minhazislamnafi/KEEBY60-20/DOCS/Screenshot 2026-05-22 185201 - Copy.png

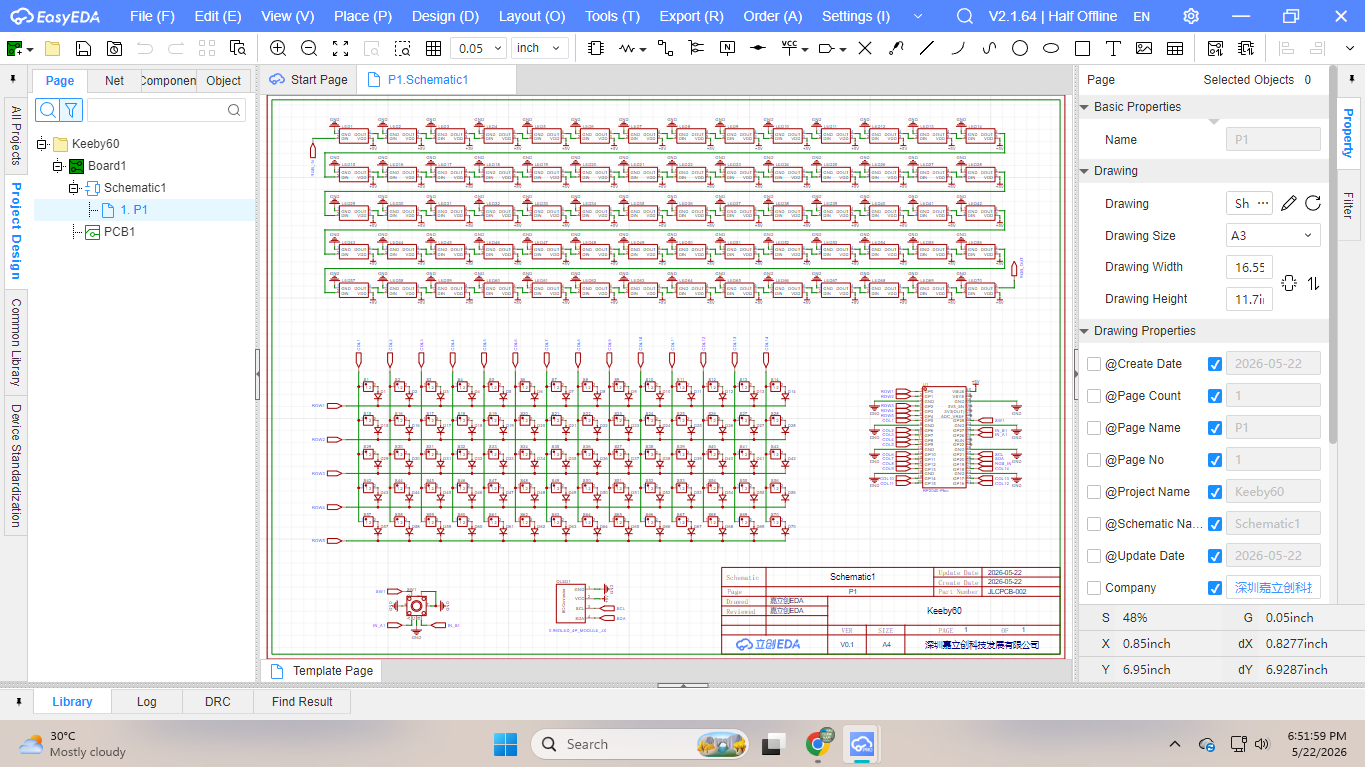
DOCS/Screenshot 2026-05-22 185201 - Copy.png
