minhazislamnafi/KEEBY60-20/DOCS/Screenshot 2026-05-22 223106 - Copy.png

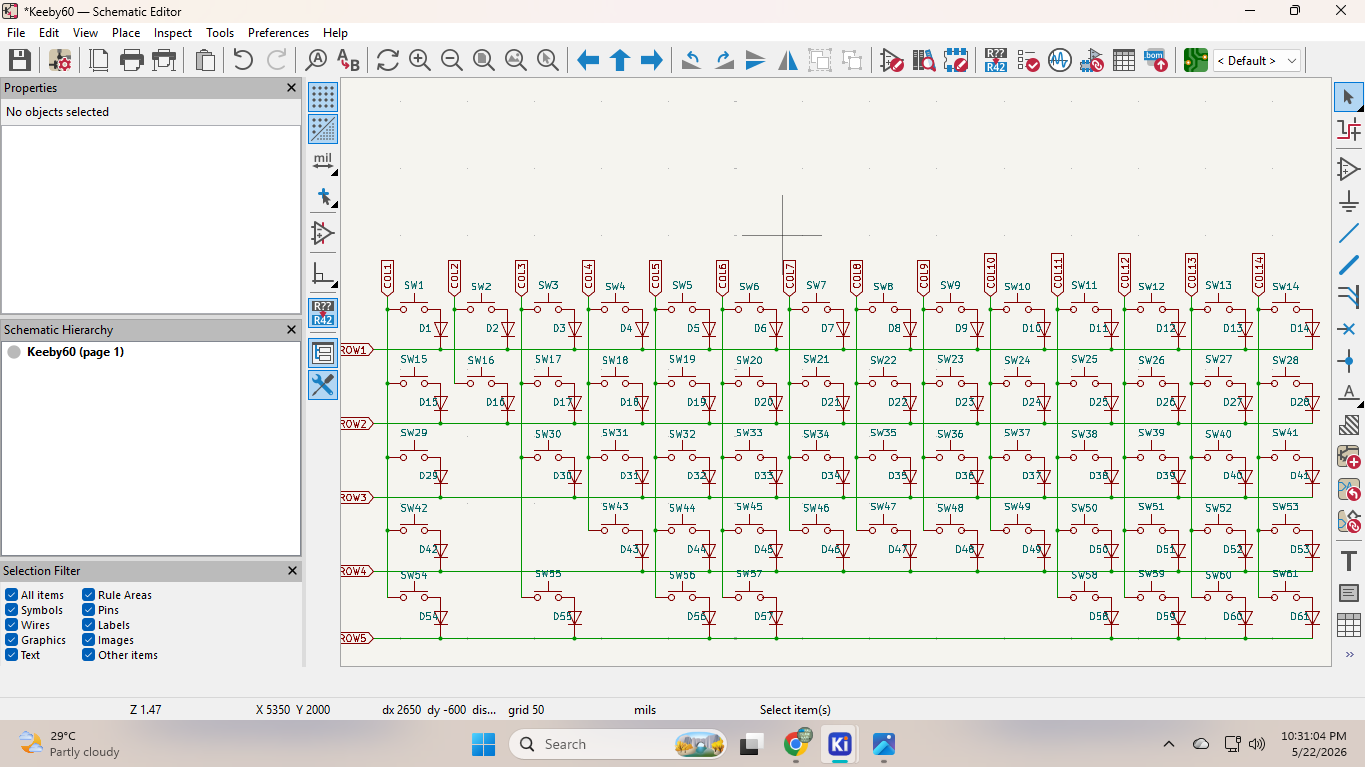
DOCS/Screenshot 2026-05-22 223106 - Copy.png
