minhazislamnafi/KEEBY60-20/DOCS/Screenshot 2026-05-23 002941 - Copy.png

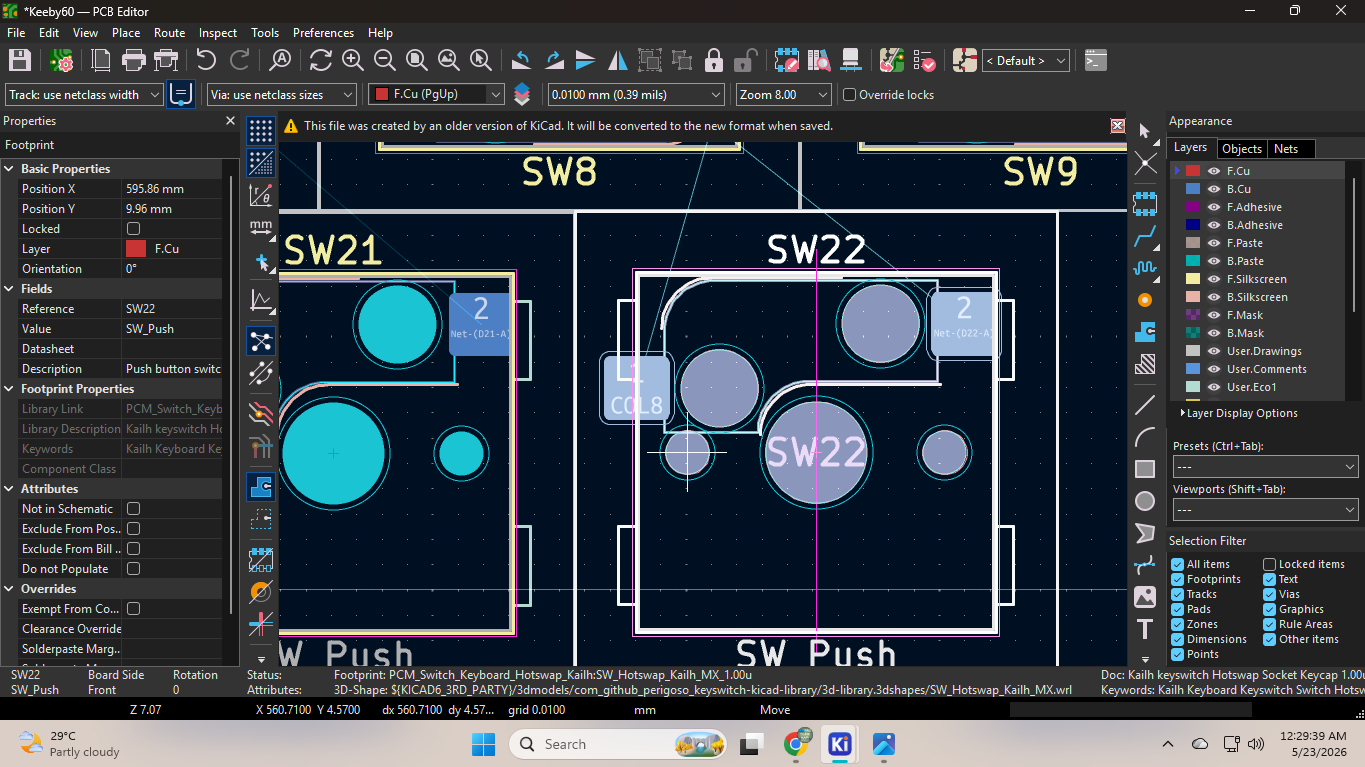
DOCS/Screenshot 2026-05-23 002941 - Copy.png
