minhazislamnafi/KEEBY60-20/DOCS/Screenshot 2026-05-23 003102 - Copy.png

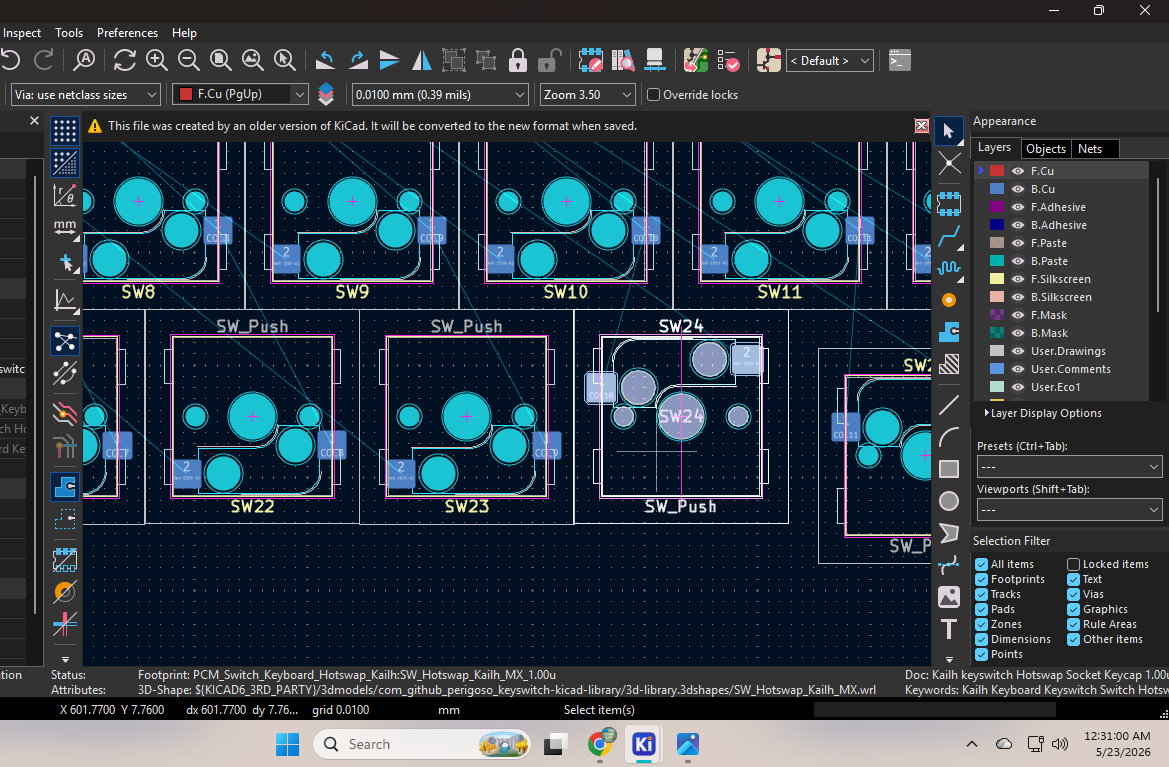
DOCS/Screenshot 2026-05-23 003102 - Copy.png
