minhazislamnafi/KEEBY60-20/DOCS/Screenshot 2026-05-23 170219.png

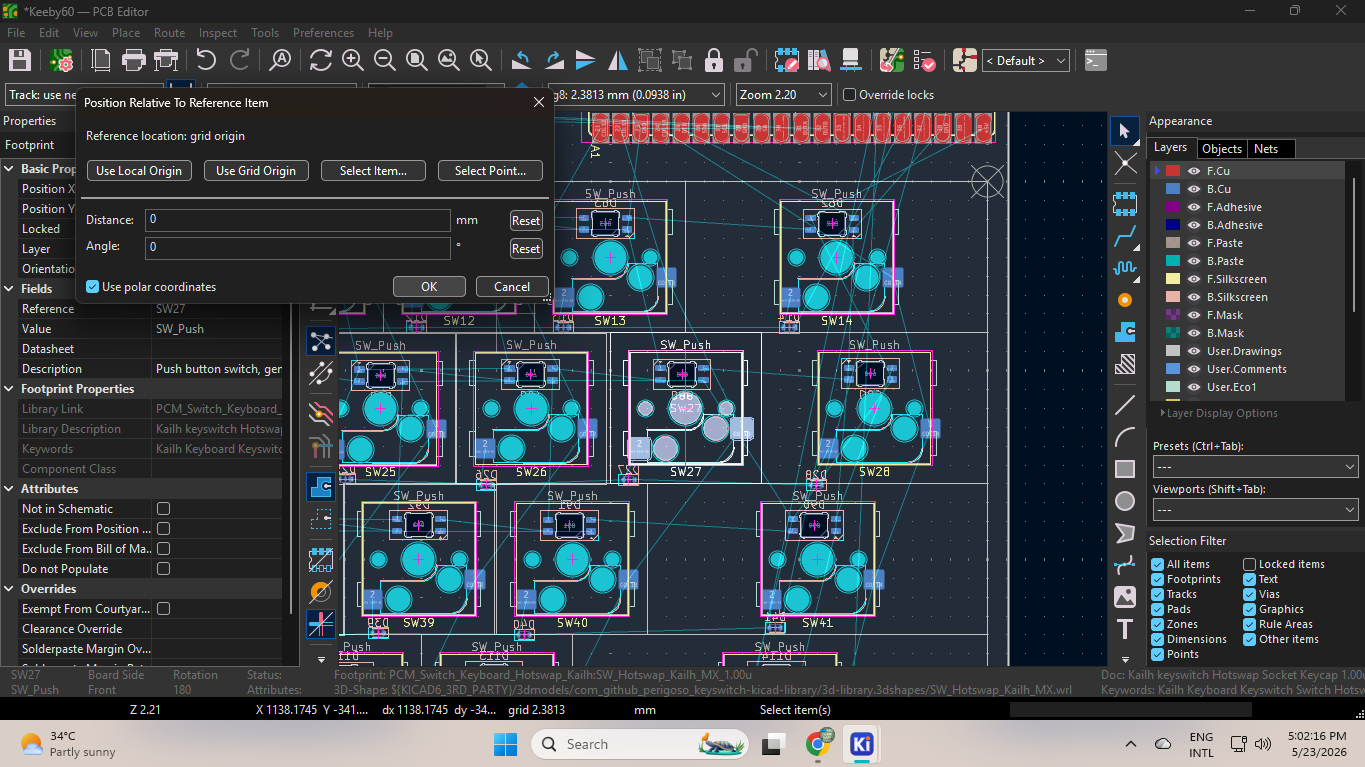
DOCS/Screenshot 2026-05-23 170219.png
