minhazislamnafi/KEEBY60-20/DOCS/Screenshot 2026-05-23 170231.png

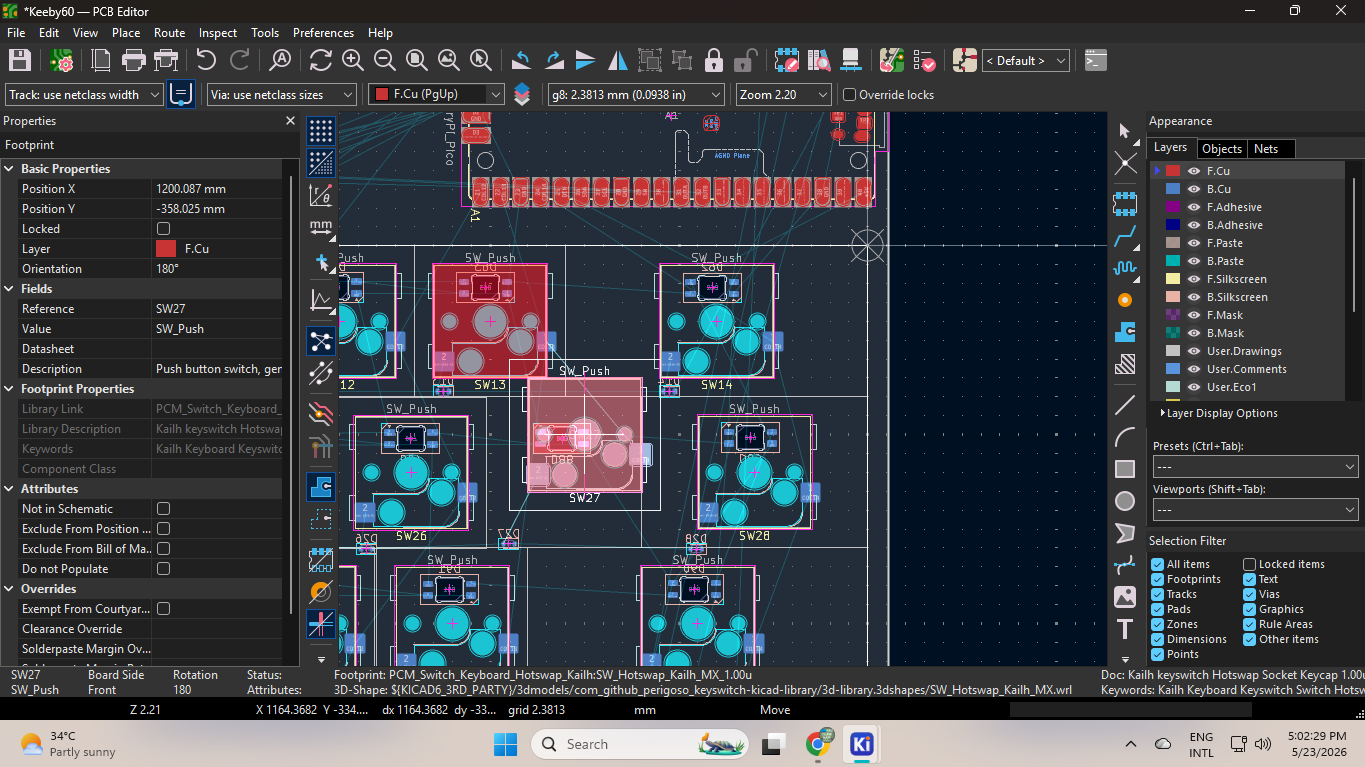
DOCS/Screenshot 2026-05-23 170231.png
