minhazislamnafi/KEEBY60-20/DOCS/Screenshot 2026-05-24 041032.png

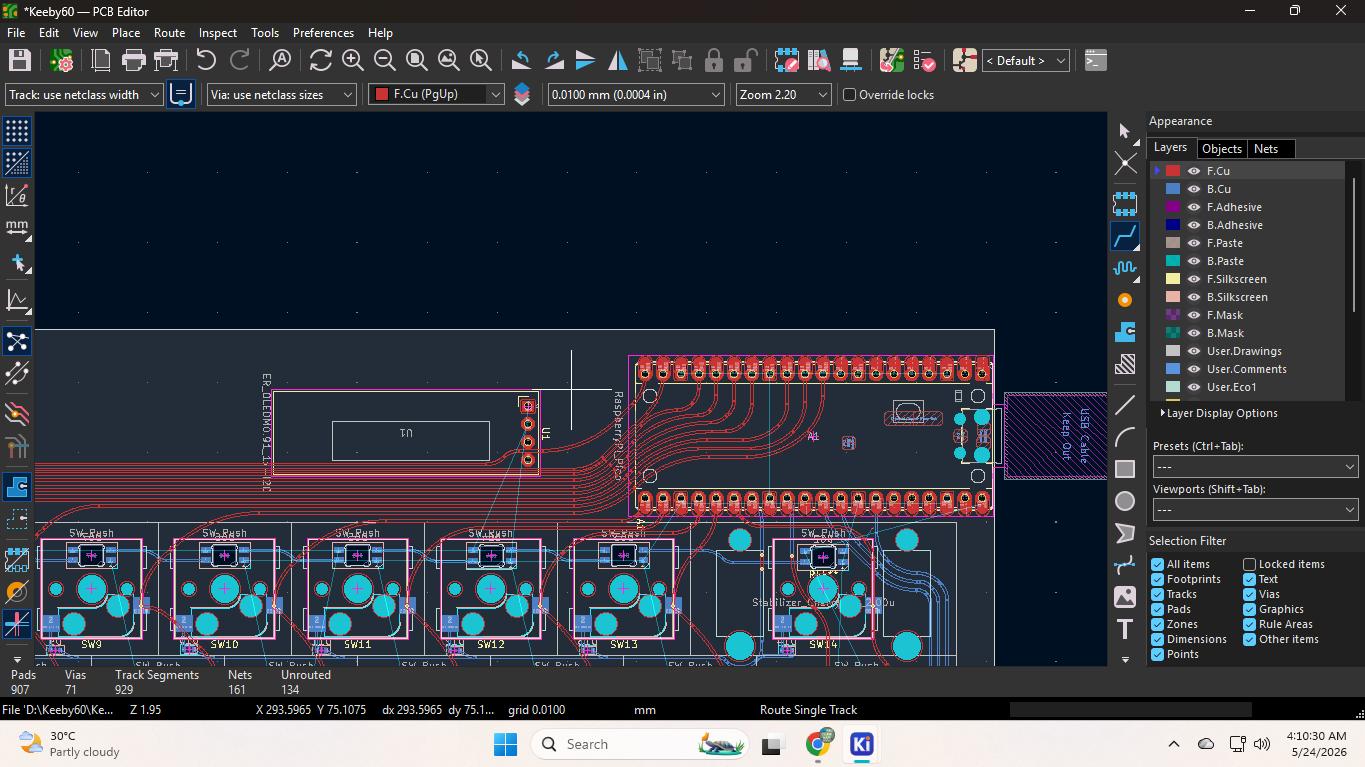
DOCS/Screenshot 2026-05-24 041032.png
