minhazislamnafi/KEEBY60-20/DOCS/Screenshot 2026-05-25 170520.png

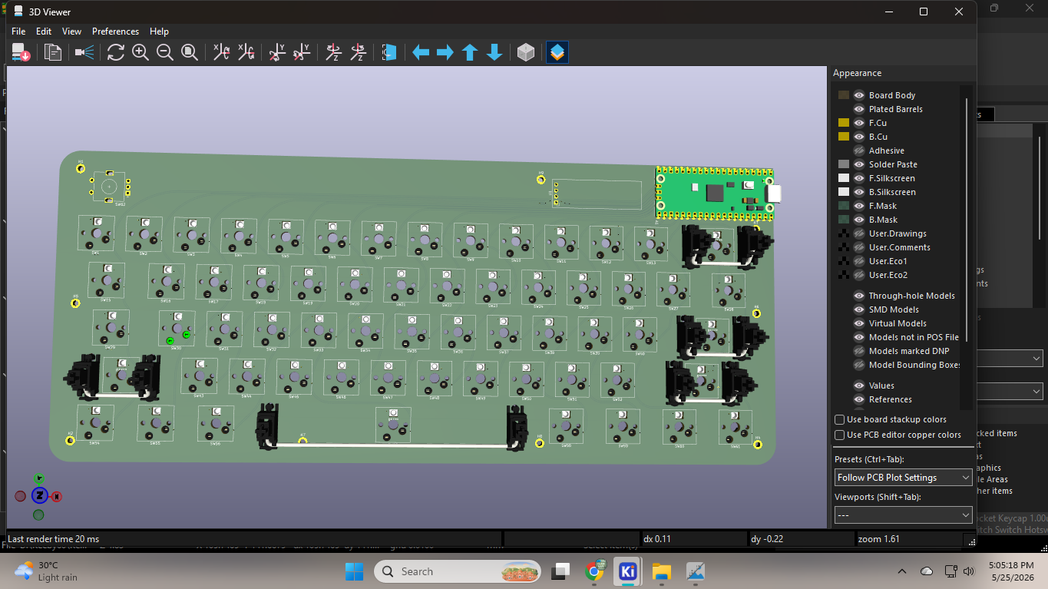
DOCS/Screenshot 2026-05-25 170520.png
