minhazislamnafi/KEEBY60-20/DOCS/Screenshot 2026-05-25 233830.png

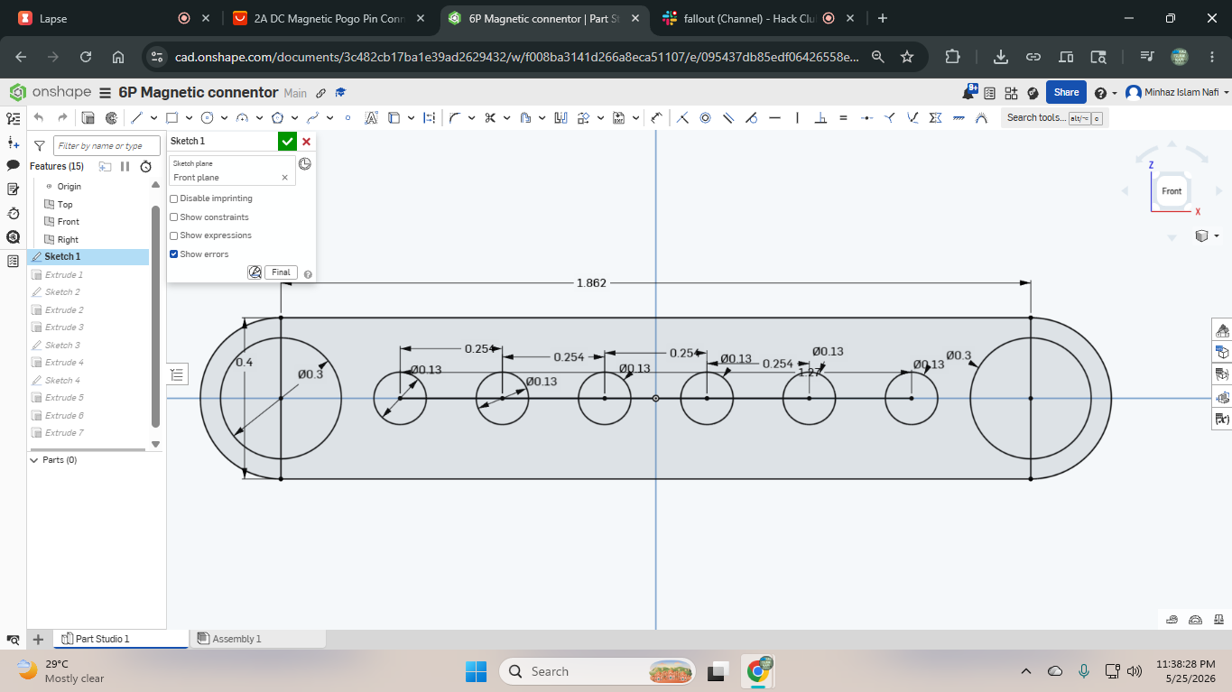
DOCS/Screenshot 2026-05-25 233830.png
