minhazislamnafi/KEEBY60-20/DOCS/Screenshot 2026-05-26 022730.png

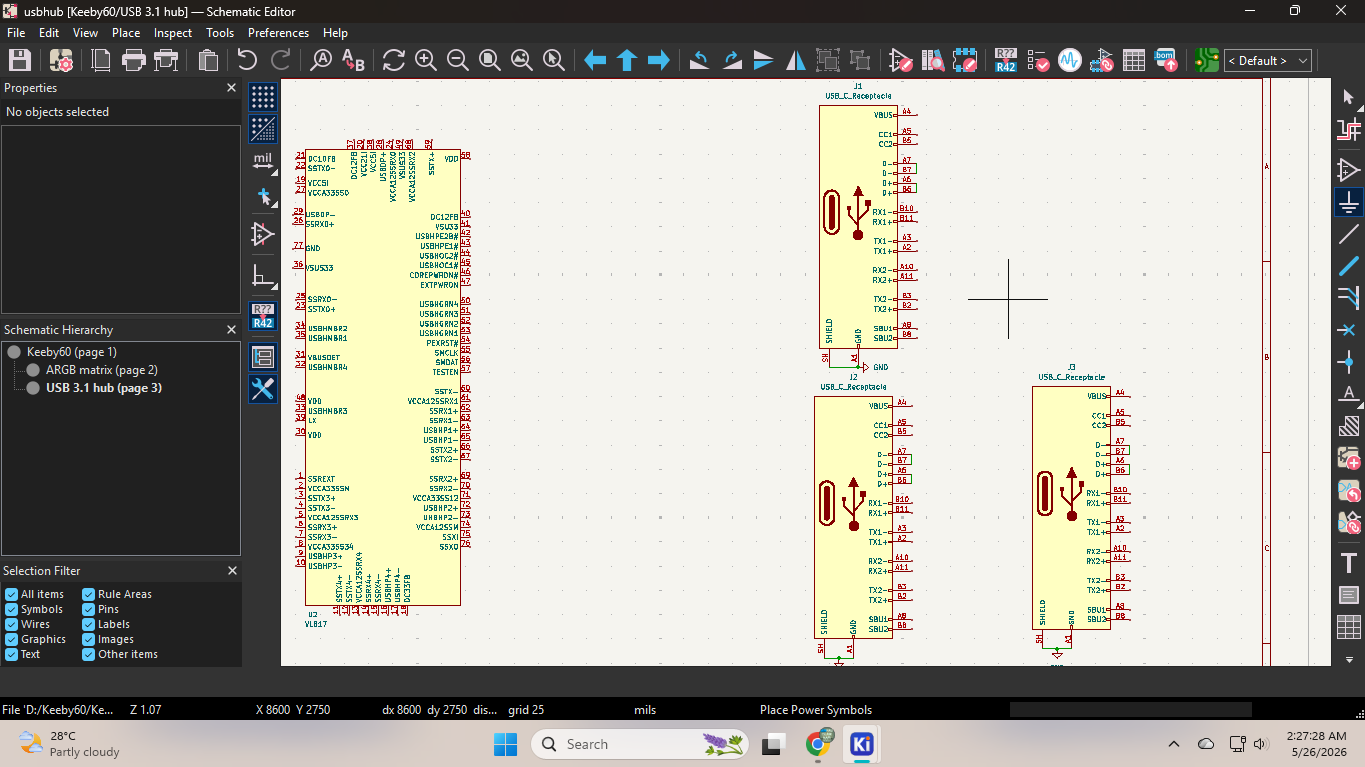
DOCS/Screenshot 2026-05-26 022730.png
