minhazislamnafi/KEEBY60-20/DOCS/Screenshot 2026-05-26 030540.png

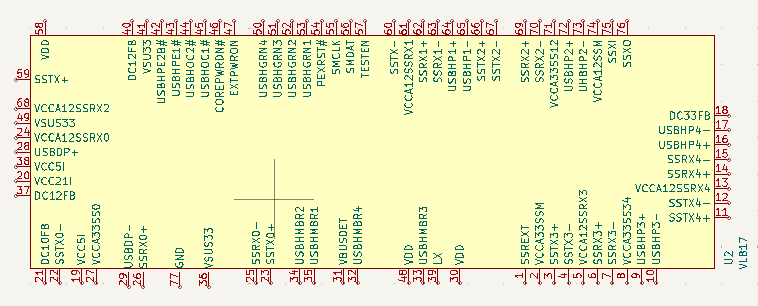
DOCS/Screenshot 2026-05-26 030540.png
