minhazislamnafi/KEEBY60-20/DOCS/Screenshot 2026-05-26 162601.png

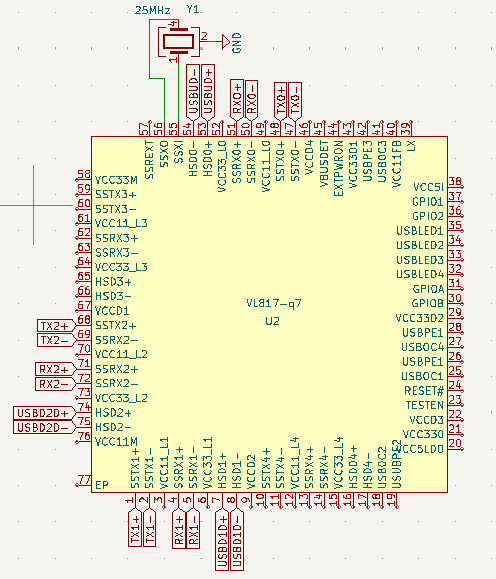
DOCS/Screenshot 2026-05-26 162601.png
