minhazislamnafi/KEEBY60-20/DOCS/Screenshot 2026-05-26 165118.png

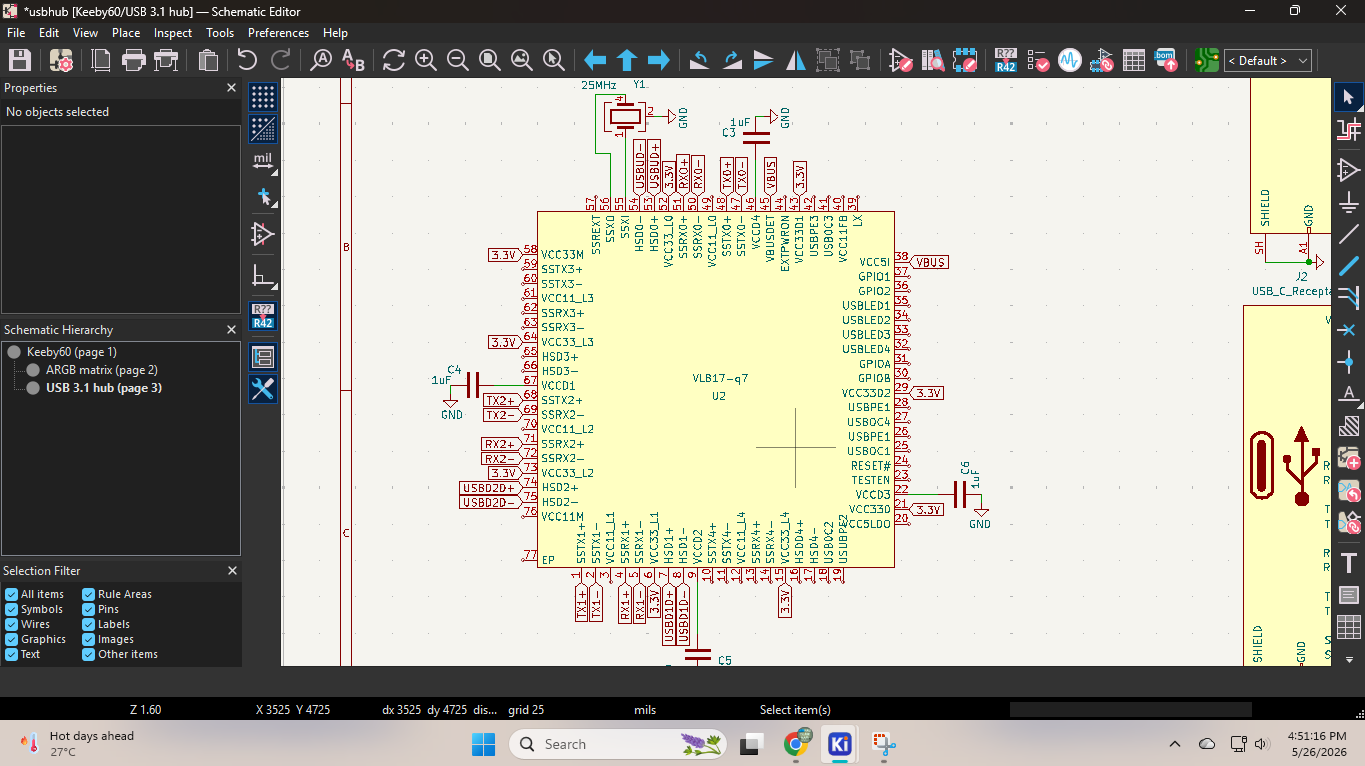
DOCS/Screenshot 2026-05-26 165118.png
