minhazislamnafi/KEEBY60-20/DOCS/Screenshot 2026-05-26 190104.png

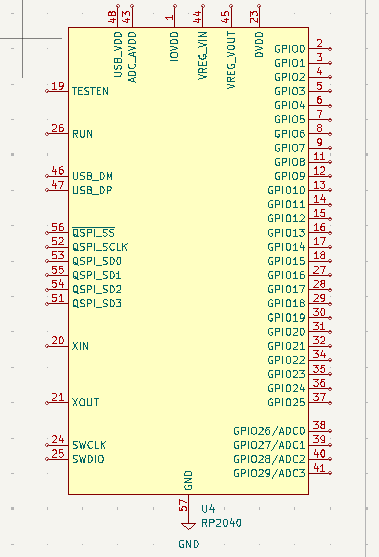
DOCS/Screenshot 2026-05-26 190104.png
