minhazislamnafi/KEEBY60-20/DOCS/Screenshot 2026-05-26 202656.png

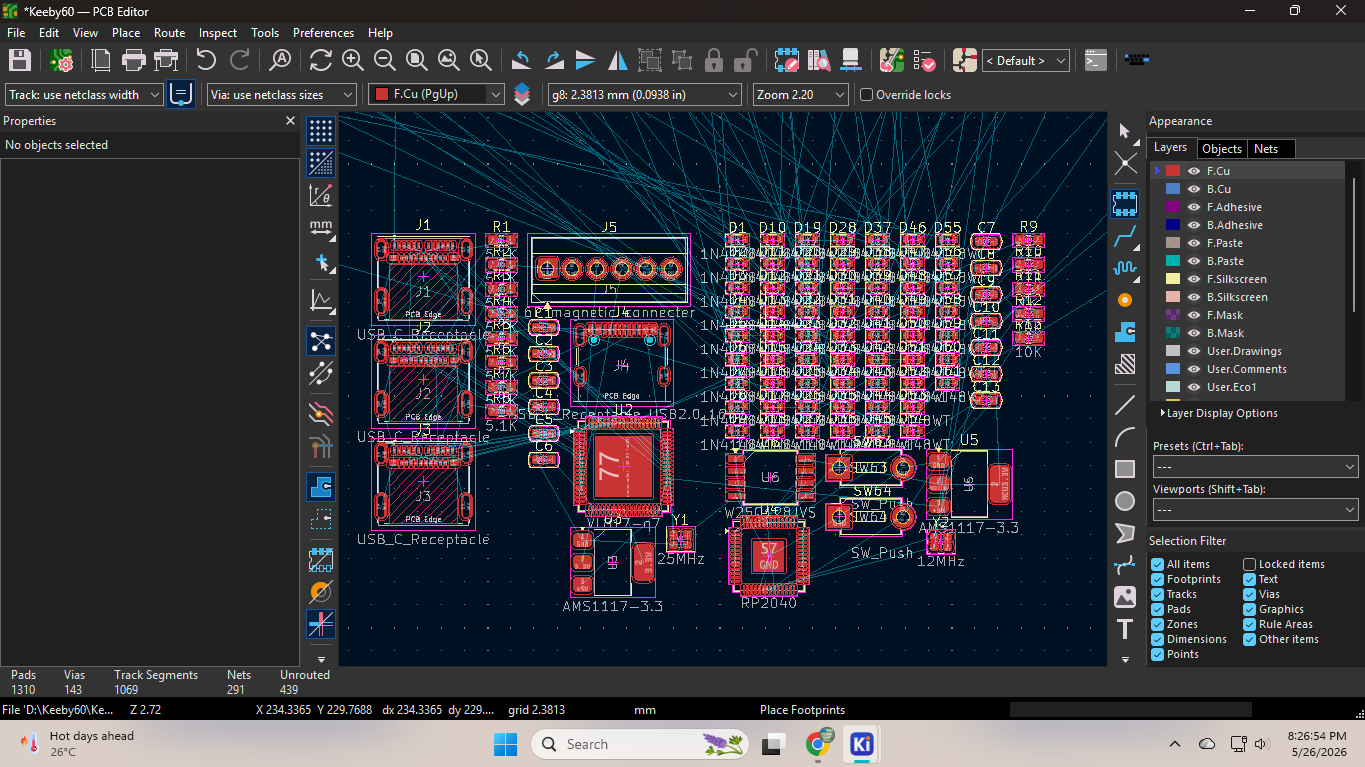
DOCS/Screenshot 2026-05-26 202656.png
