minhazislamnafi/KEEBY60-20/DOCS/Screenshot 2026-05-27 020248.png

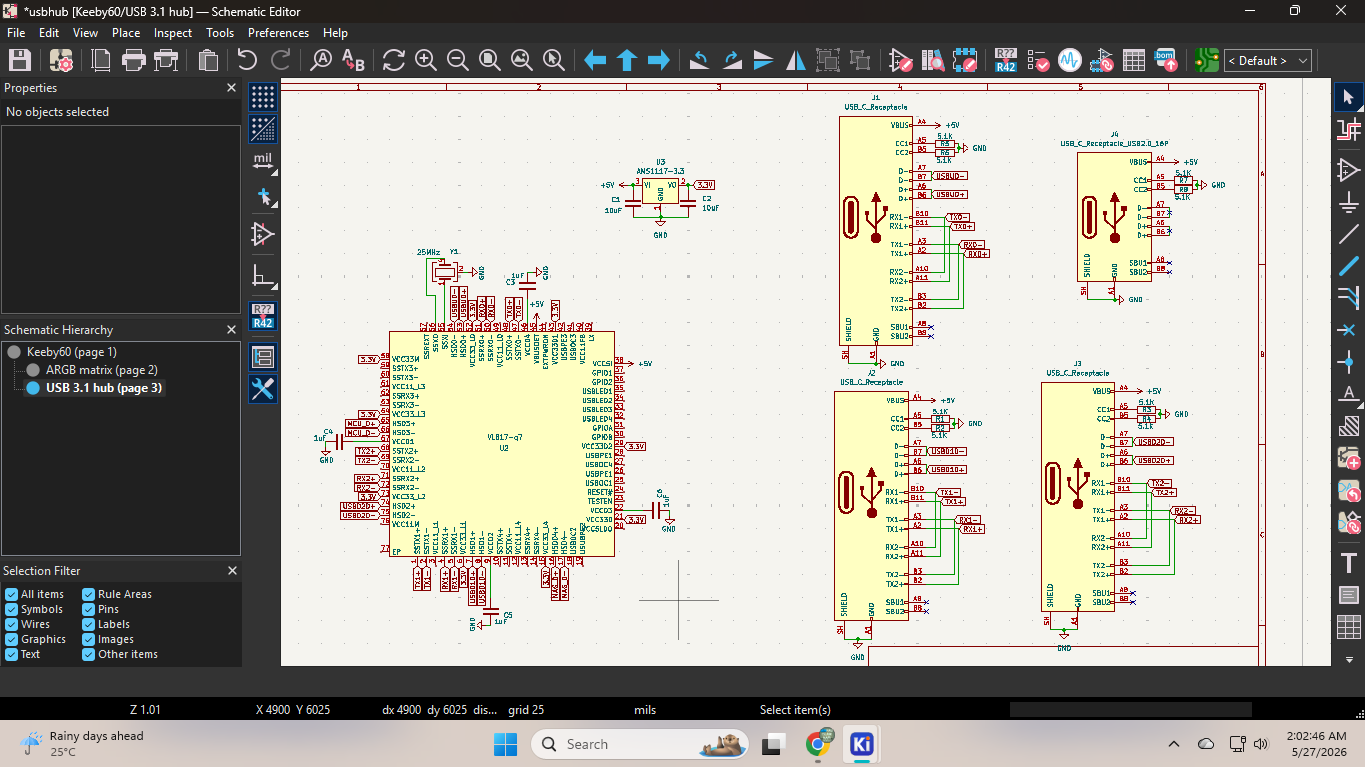
DOCS/Screenshot 2026-05-27 020248.png
