minhazislamnafi/KEEBY60-20/DOCS/Screenshot 2026-05-27 023414.png

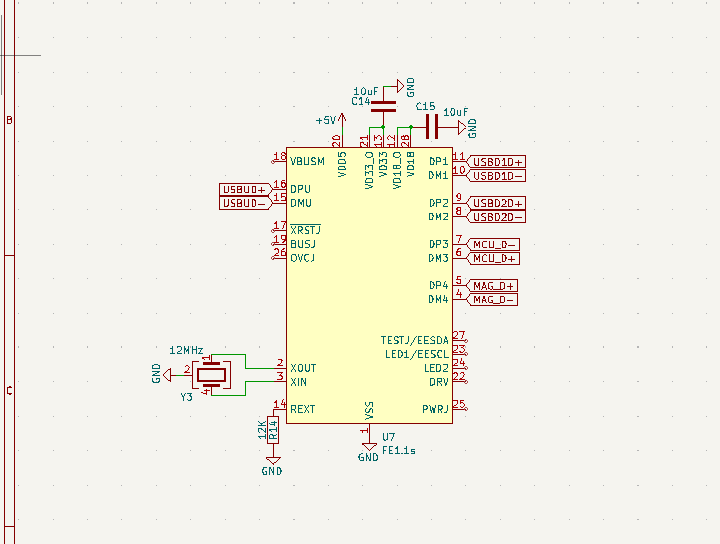
DOCS/Screenshot 2026-05-27 023414.png
