minhazislamnafi/KEEBY60-20/DOCS/Screenshot 2026-05-27 215645.png

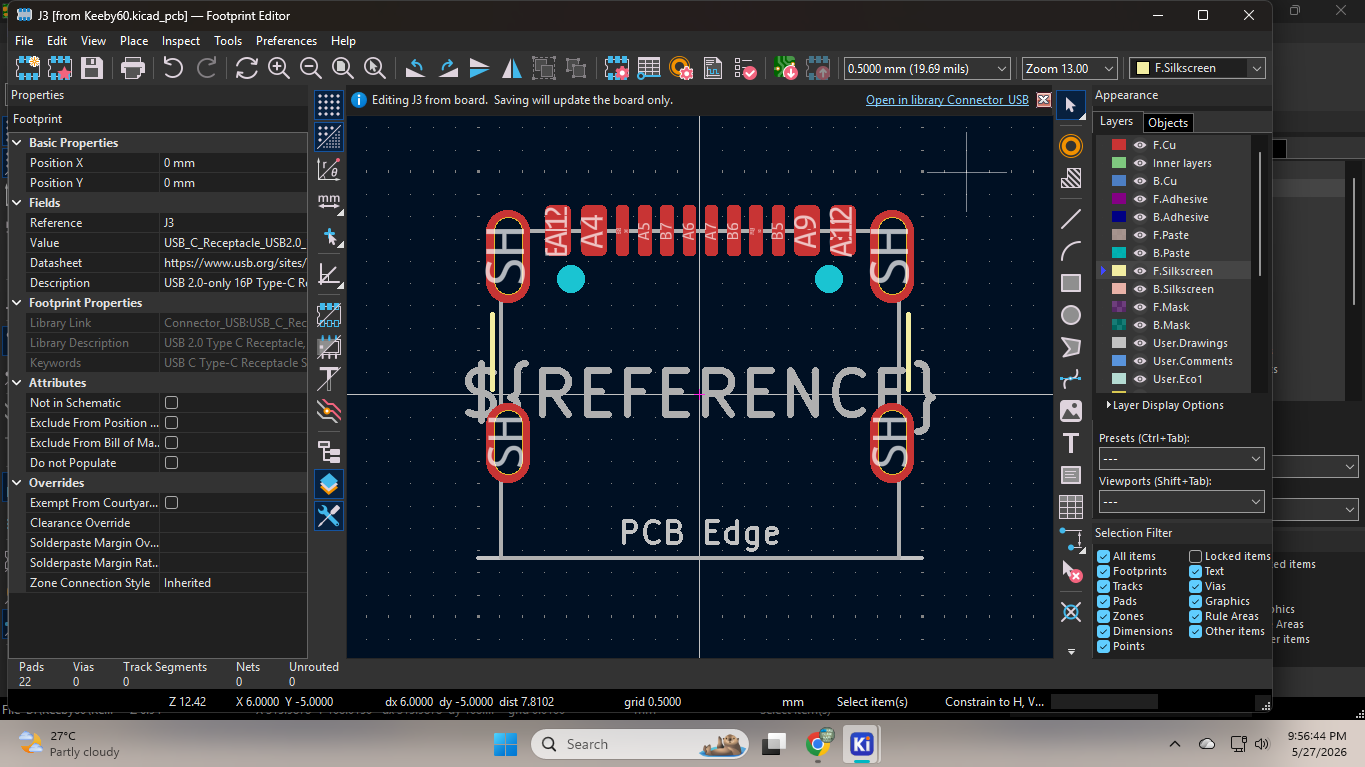
DOCS/Screenshot 2026-05-27 215645.png
