minhazislamnafi/KEEBY60-20/DOCS/Screenshot 2026-05-28 121309.png

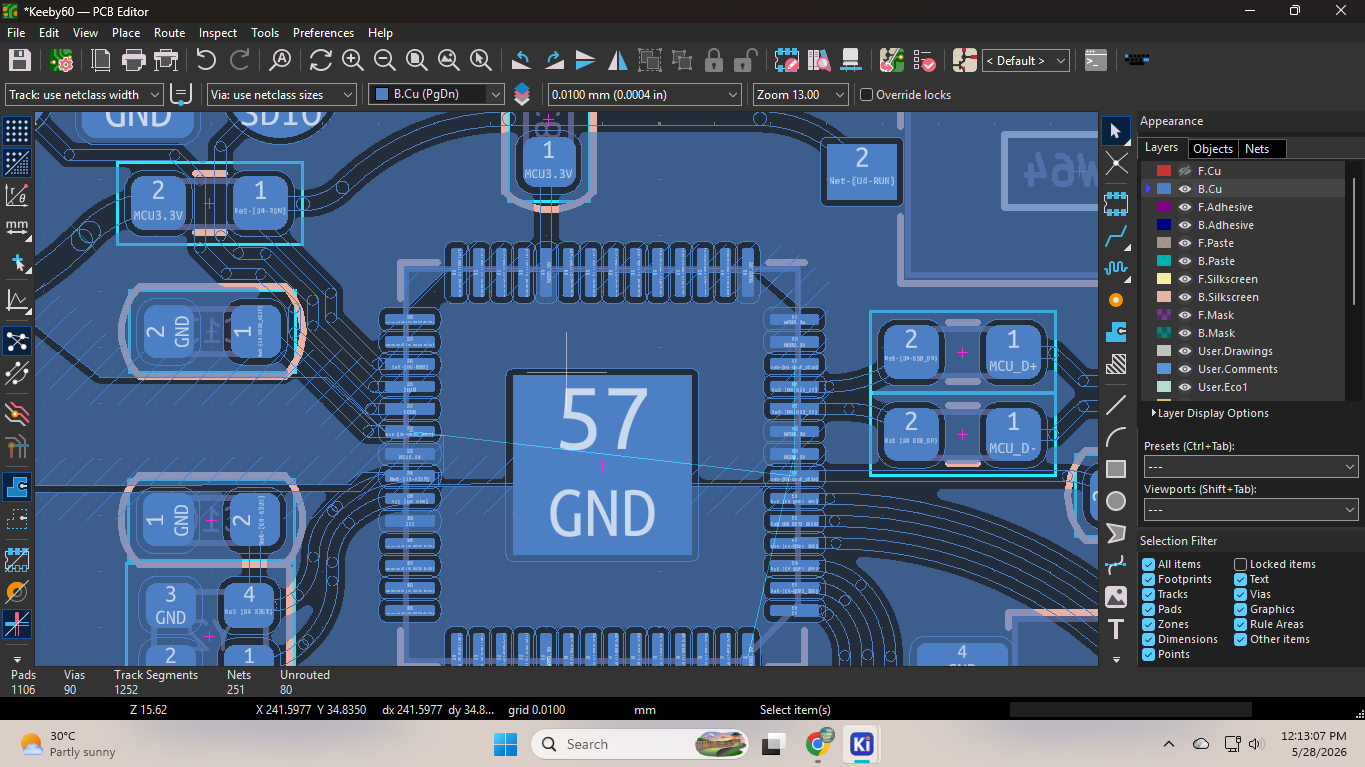
DOCS/Screenshot 2026-05-28 121309.png
