minhazislamnafi/KEEBY60-20/DOCS/Screenshot 2026-05-28 133856.png

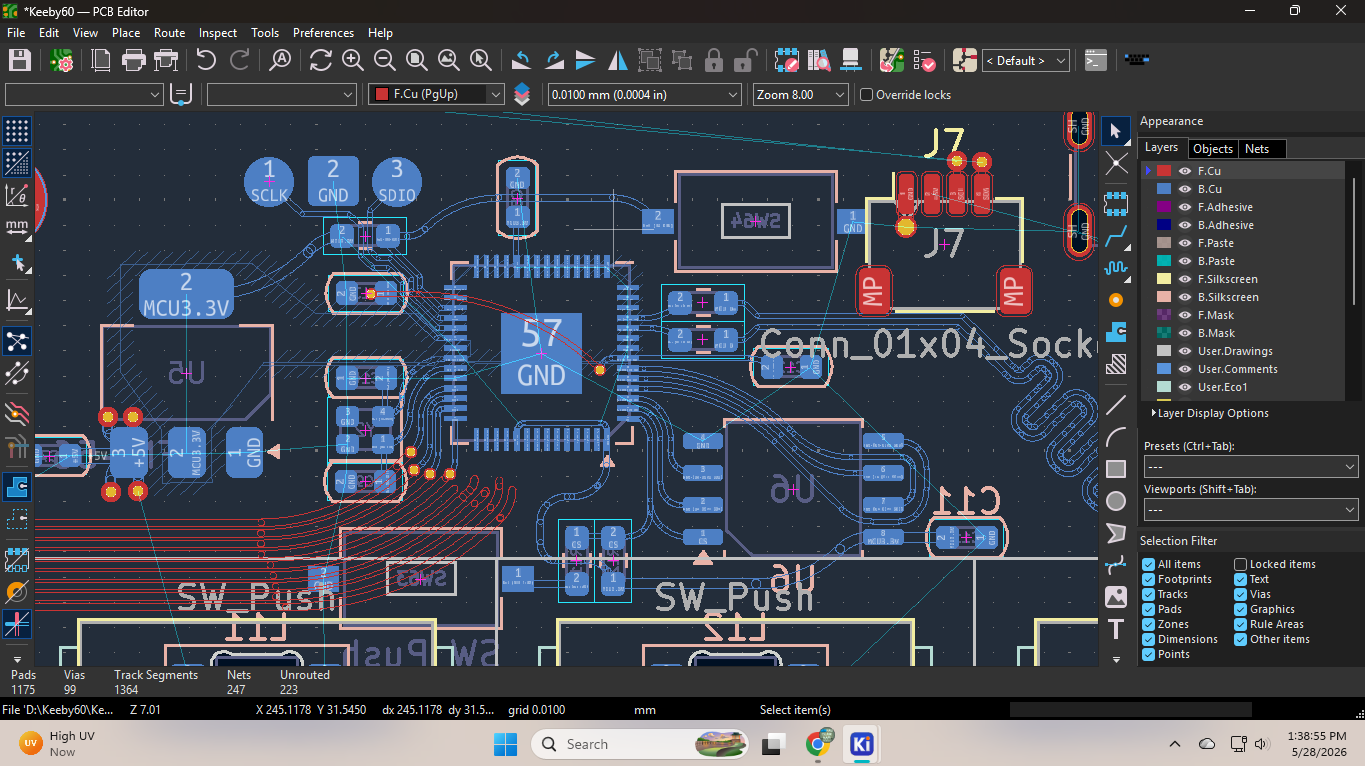
DOCS/Screenshot 2026-05-28 133856.png
