minhazislamnafi/KEEBY60-20/DOCS/Screenshot 2026-05-28 134253.png

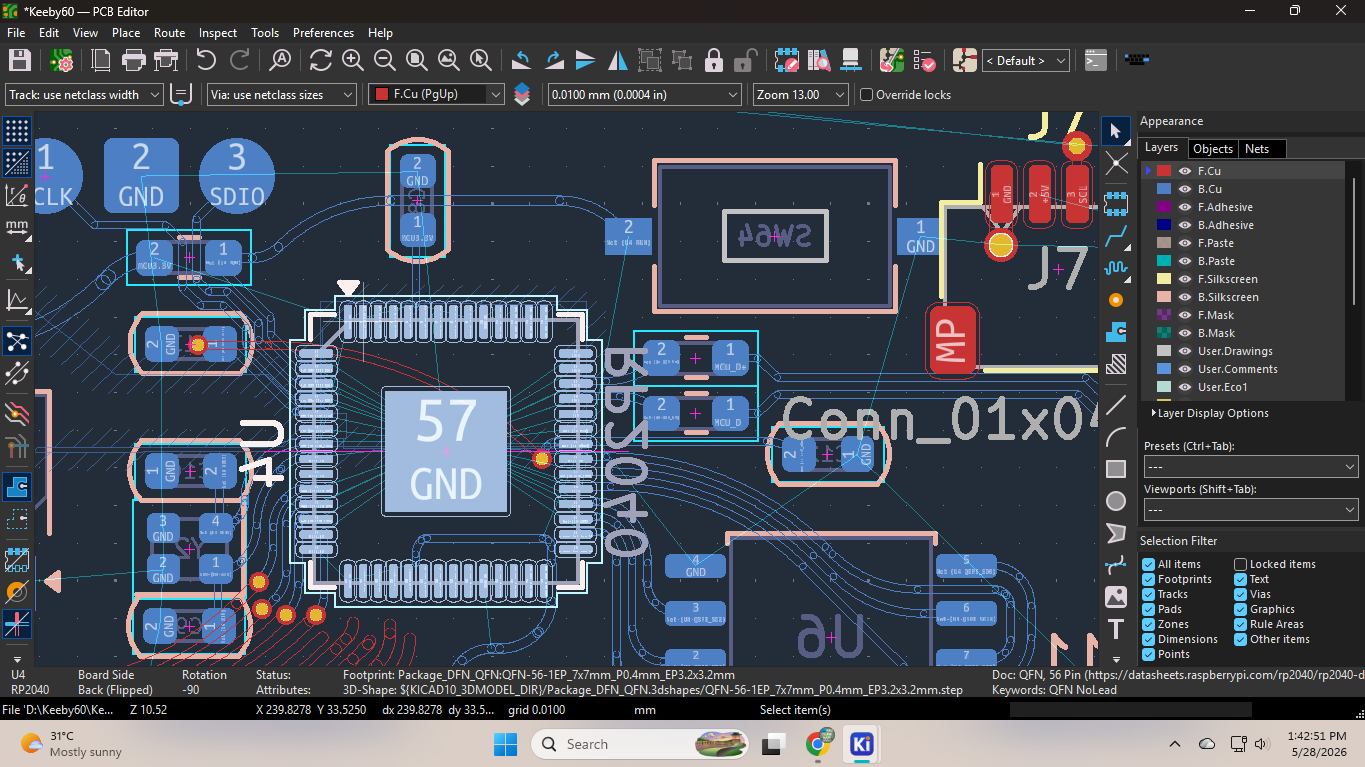
DOCS/Screenshot 2026-05-28 134253.png
