minhazislamnafi/KEEBY60-20/DOCS/Screenshot 2026-05-28 213704.png

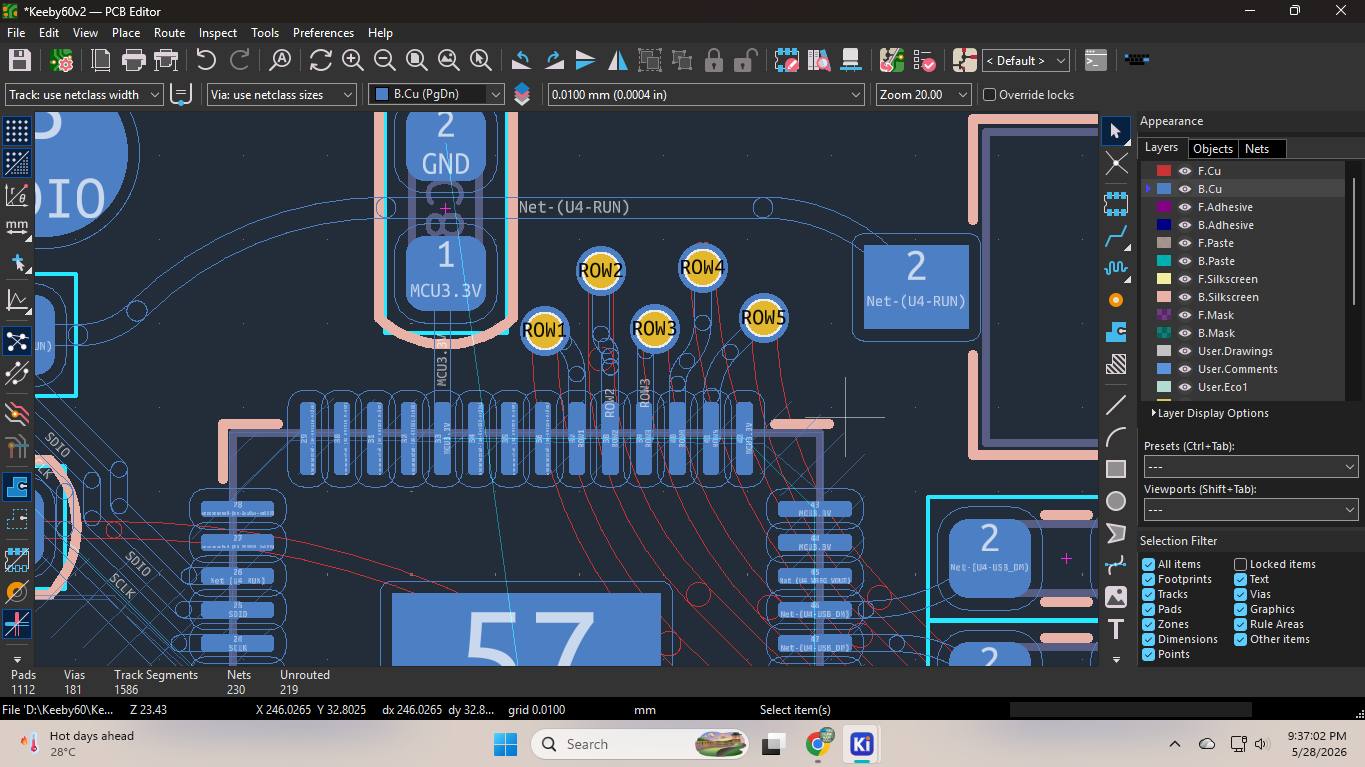
DOCS/Screenshot 2026-05-28 213704.png
