minhazislamnafi/KEEBY60-20/DOCS/Screenshot 2026-05-28 215839.png

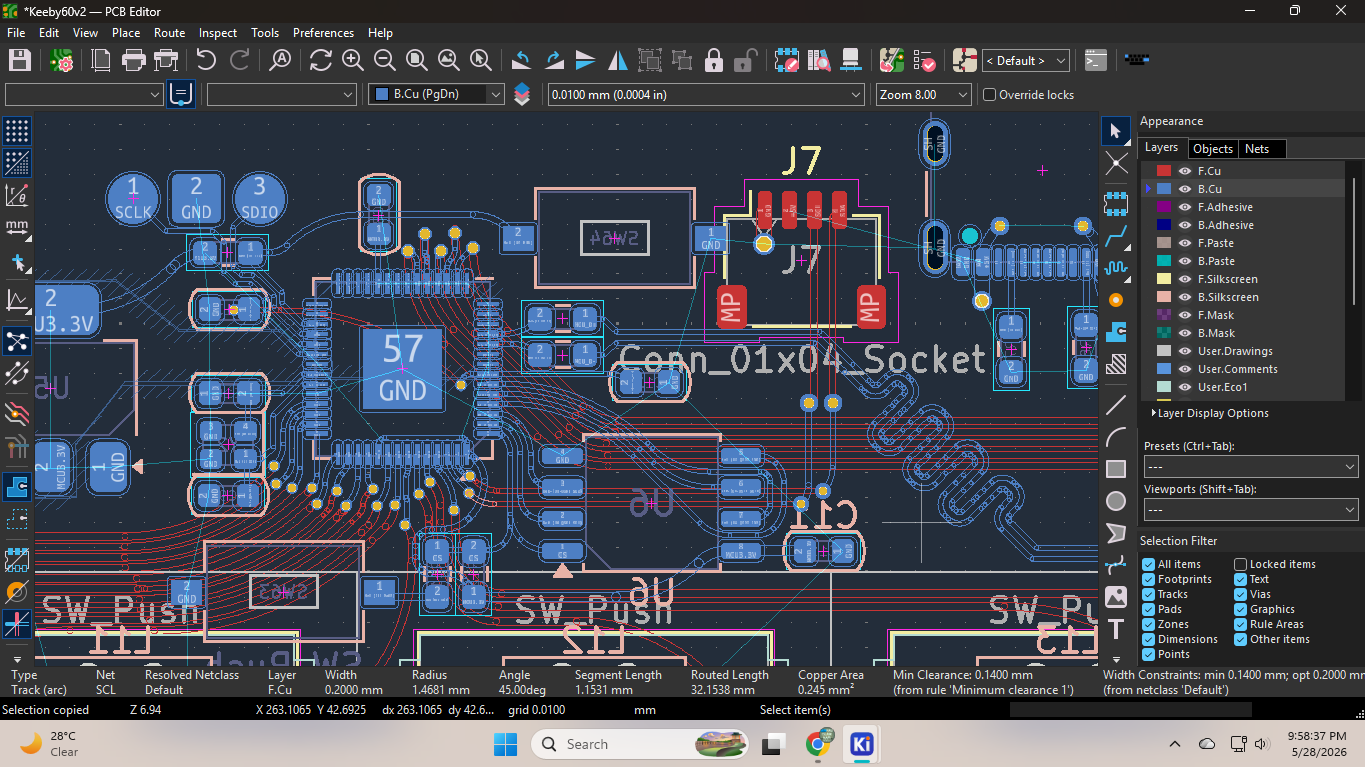
DOCS/Screenshot 2026-05-28 215839.png
