minhazislamnafi/KEEBY60-20/DOCS/Screenshot 2026-05-28 235259.png

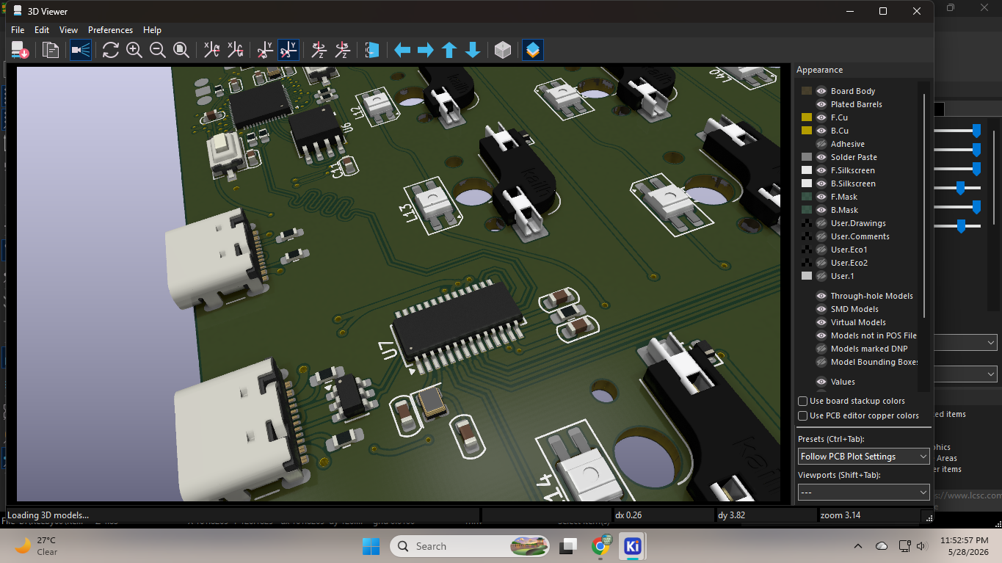
DOCS/Screenshot 2026-05-28 235259.png
