minhazislamnafi/KEEBY60-20/DOCS/Screenshot 2026-05-30 151340.png

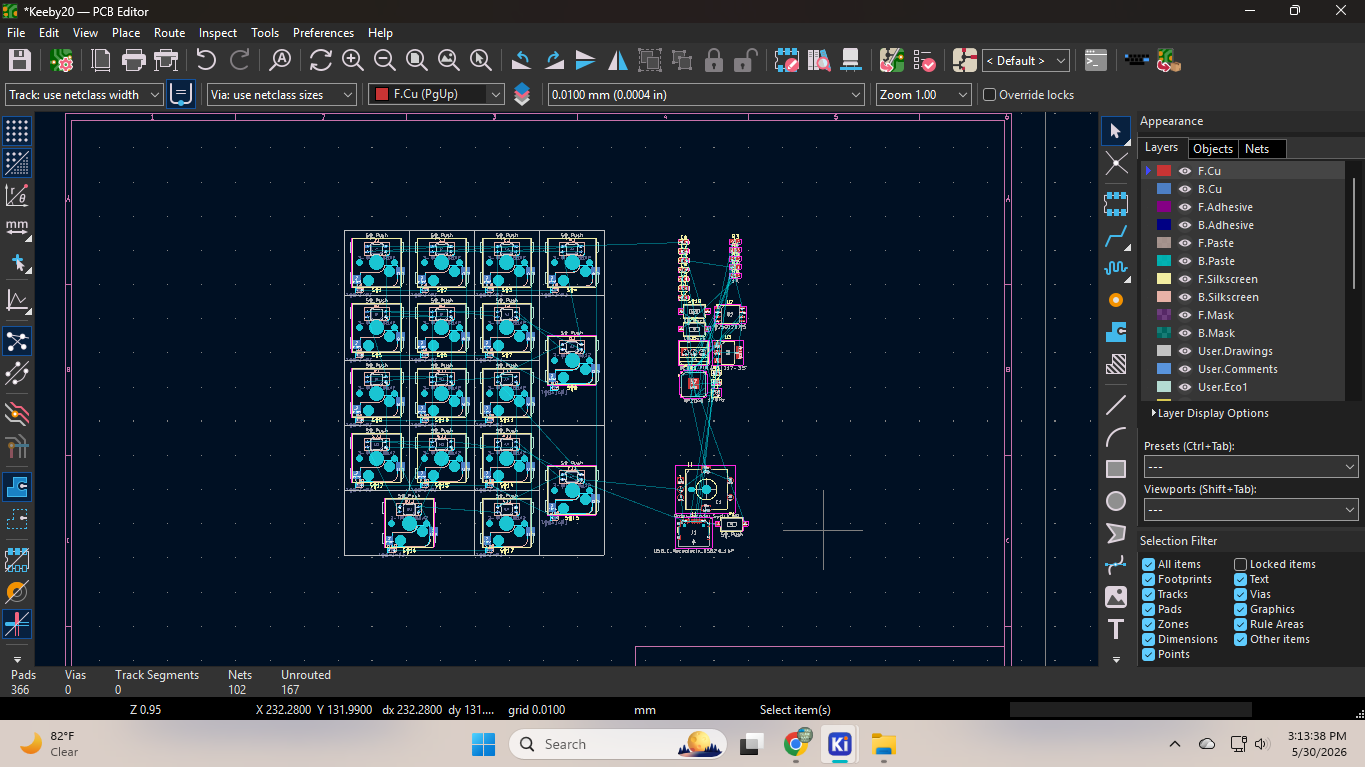
DOCS/Screenshot 2026-05-30 151340.png
