minhazislamnafi/KEEBY60-20/DOCS/Screenshot 2026-05-30 162723.png

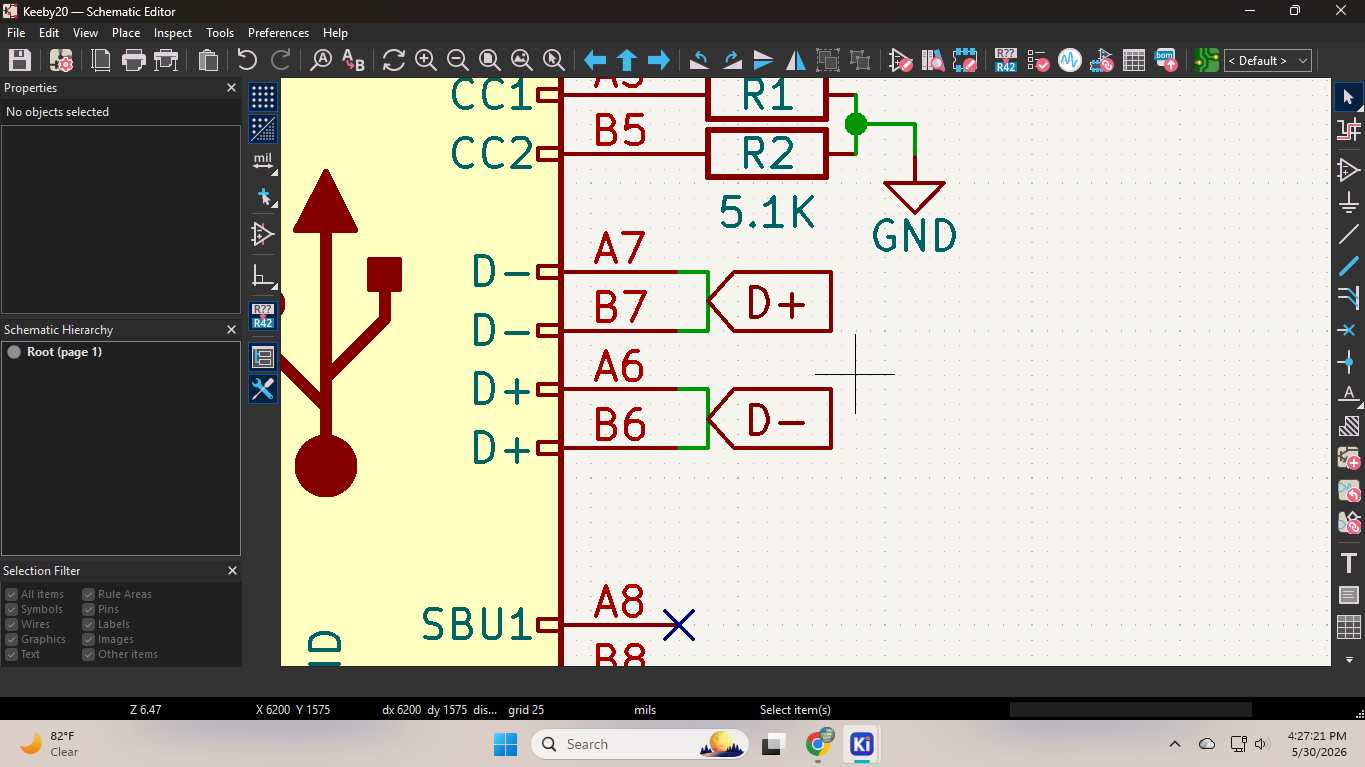
DOCS/Screenshot 2026-05-30 162723.png
