minhazislamnafi/KEEBY60-20/DOCS/Screenshot 2026-05-31 065644.png

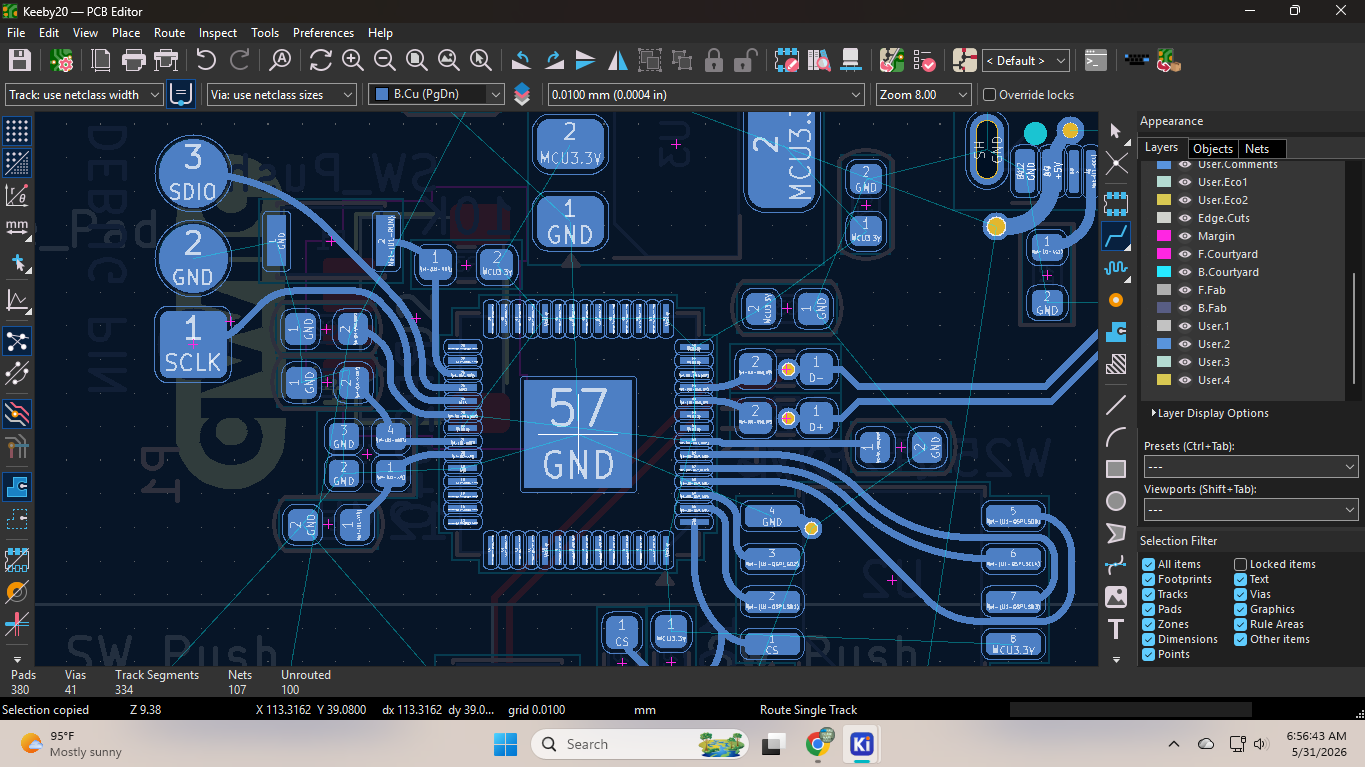
DOCS/Screenshot 2026-05-31 065644.png
