minhazislamnafi/KEEBY60-20/DOCS/Screenshot 2026-05-31 085939.png

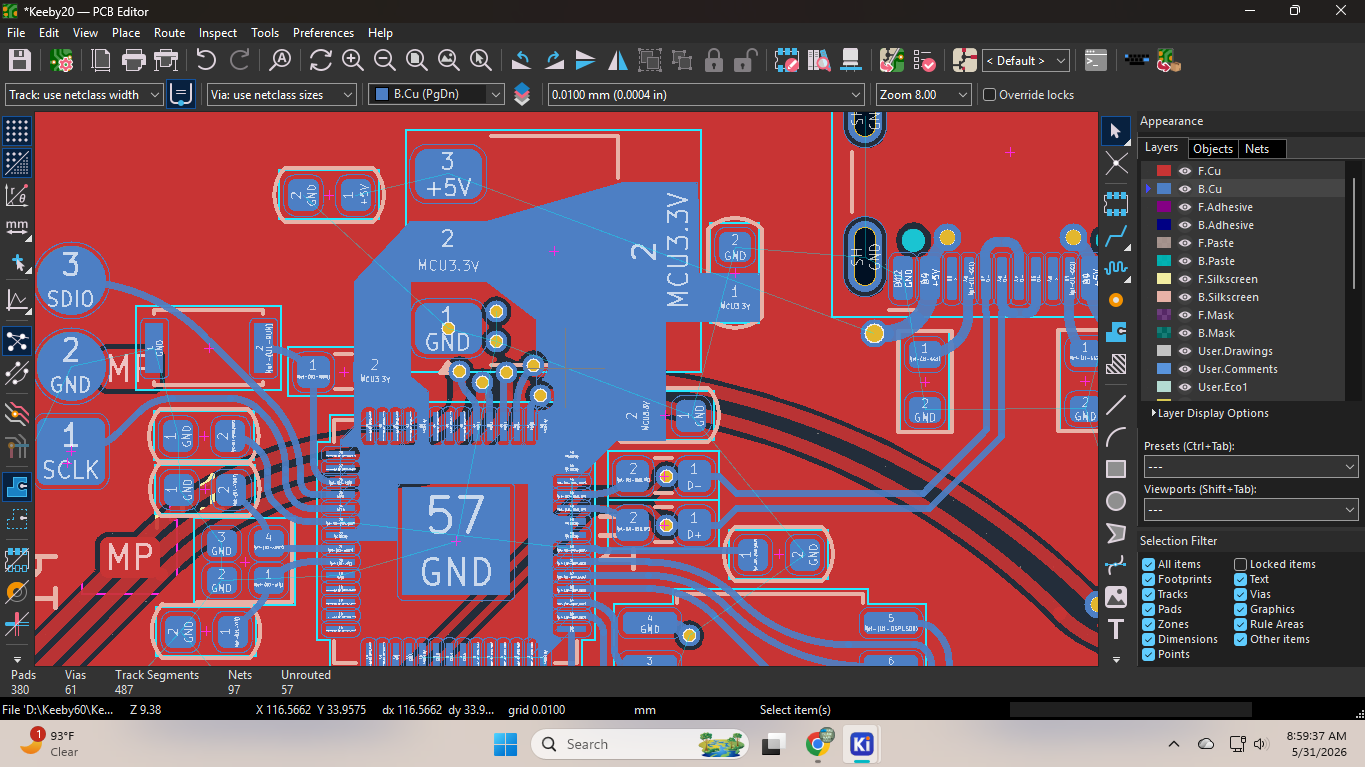
DOCS/Screenshot 2026-05-31 085939.png
