minhazislamnafi/KEEBY60-20/DOCS/Screenshot 2026-06-03 063144.png

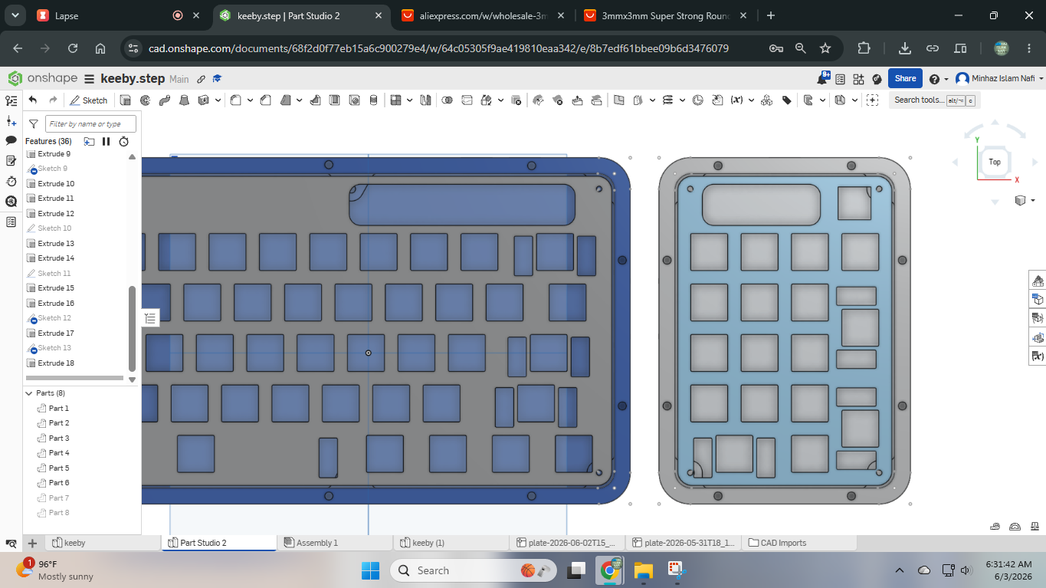
DOCS/Screenshot 2026-06-03 063144.png
