minhazislamnafi/KEEBY60-20/DOCS/Screenshot 2026-06-03 101220.png

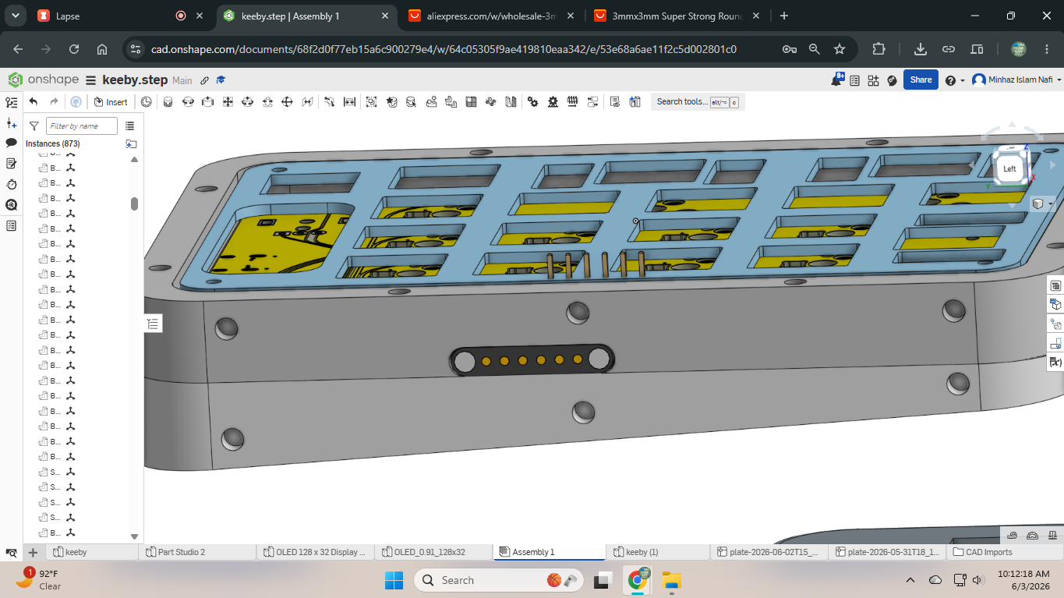
DOCS/Screenshot 2026-06-03 101220.png
