minhazislamnafi/KEEBY60-20/DOCS/Screenshot 2026-06-04 061648.png

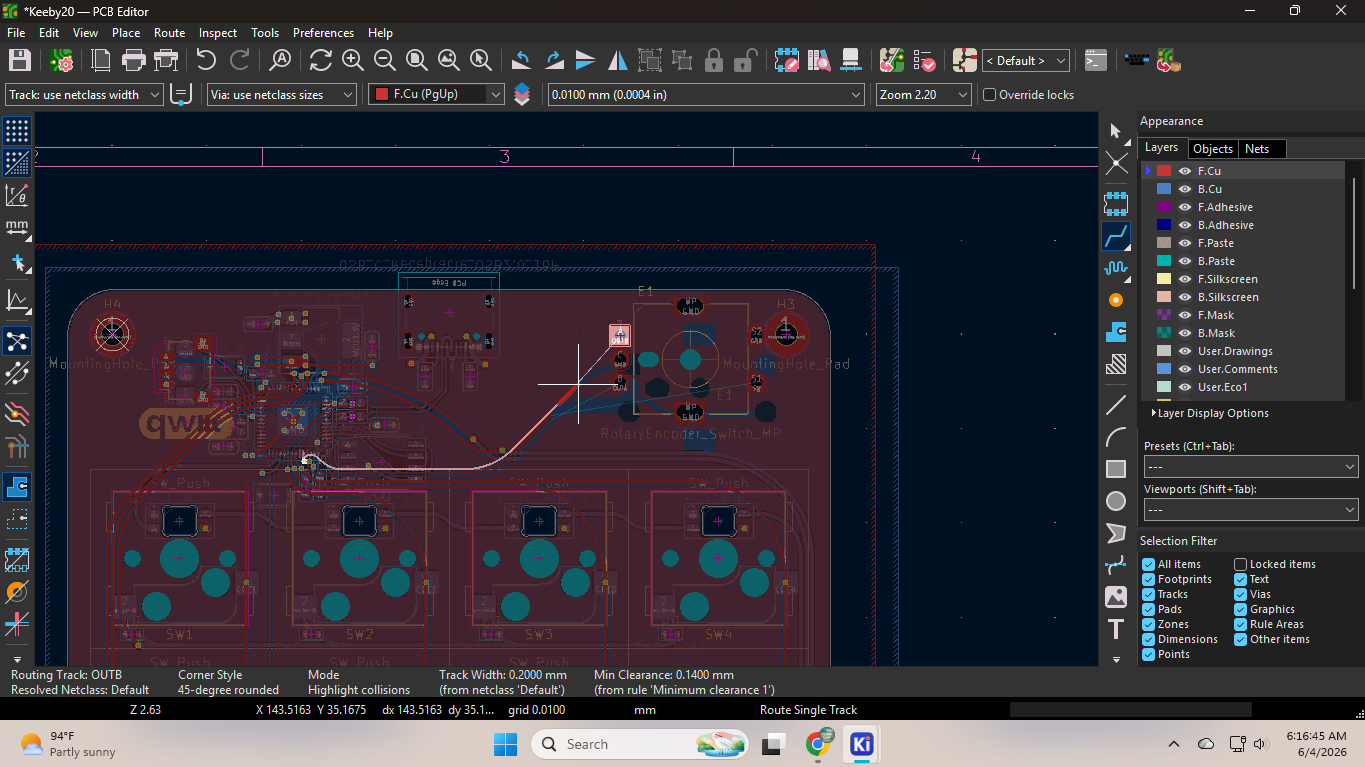
DOCS/Screenshot 2026-06-04 061648.png
