minhazislamnafi/KEEBY60-20/DOCS/Screenshot 2026-06-04 064618.png

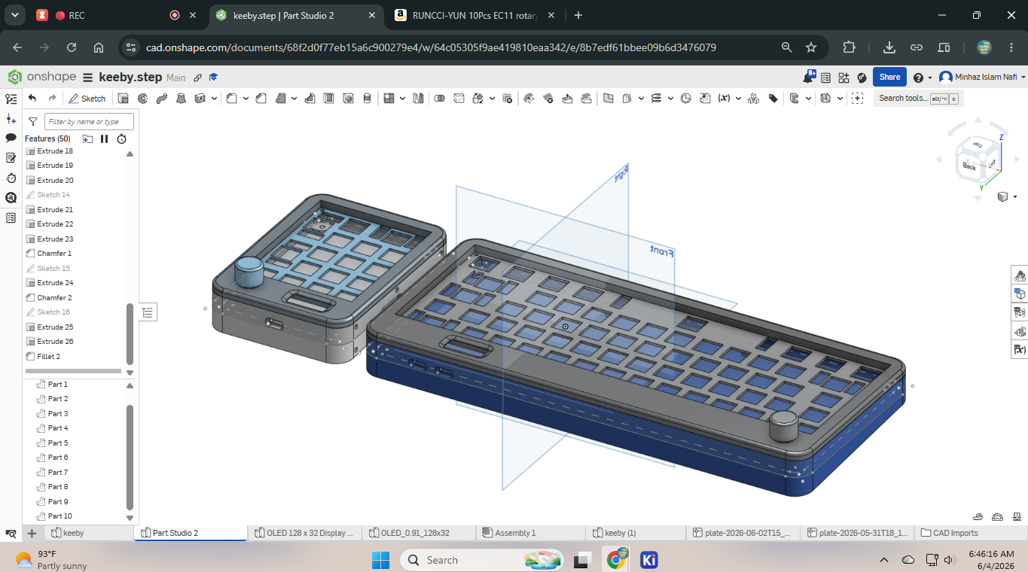
DOCS/Screenshot 2026-06-04 064618.png
