minhazislamnafi/KEEBY60-20/DOCS/Screenshot 2026-06-04 071852.png

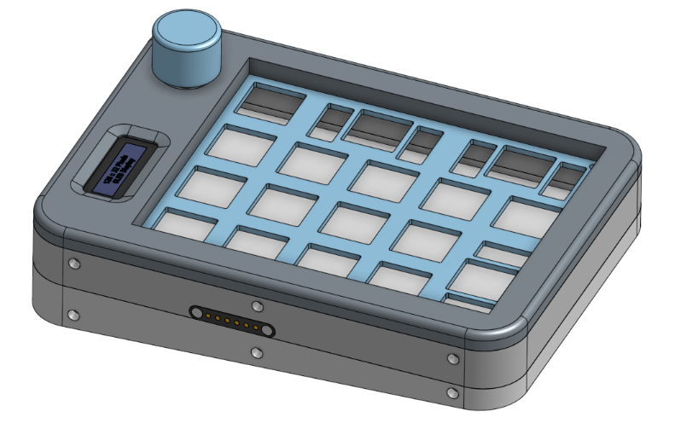
DOCS/Screenshot 2026-06-04 071852.png
