minhazislamnafi/KEEBY60-20/DOCS/Screenshot 2026-06-06 115132.png

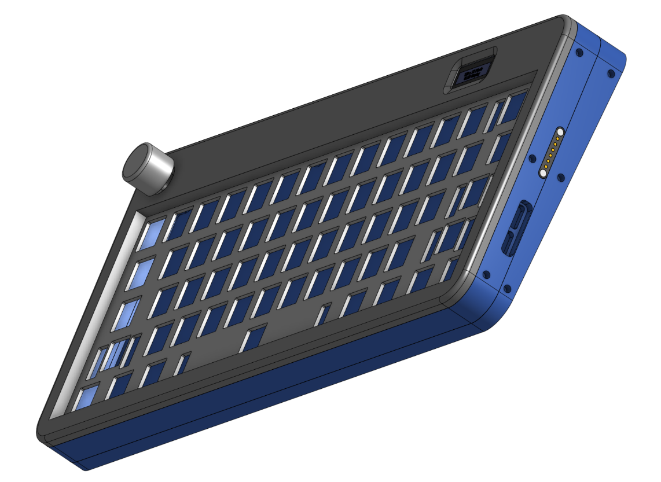
DOCS/Screenshot 2026-06-06 115132.png
