minhazislamnafi/KEEBY60-20/DOCS/Screenshot 2026-06-06 115258.png

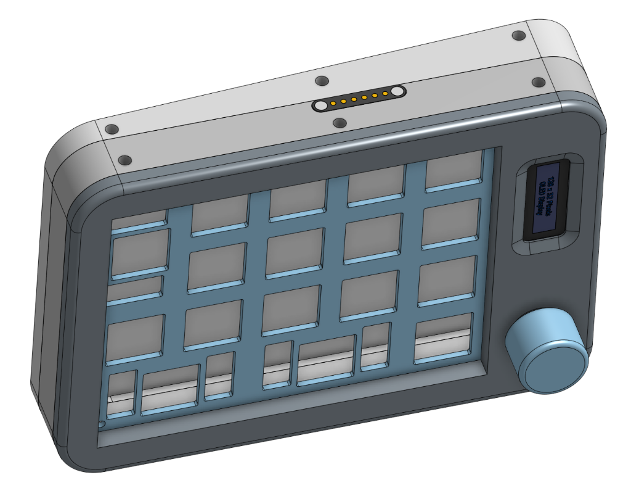
DOCS/Screenshot 2026-06-06 115258.png
