minhazislamnafi/KEEBY60-20/DOCS/Screenshot 2026-06-07 144537.png

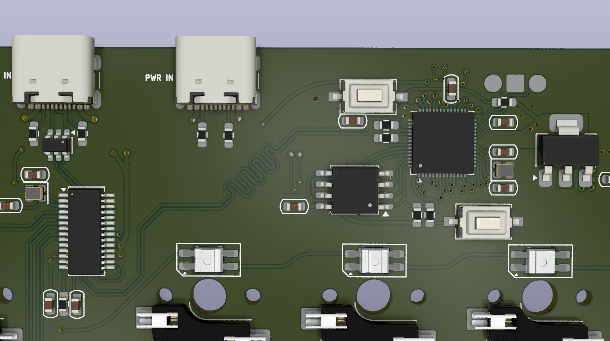
DOCS/Screenshot 2026-06-07 144537.png
