minhazislamnafi/KEEBY60-20/DOCS/Screenshot 2026-06-07 151941.png

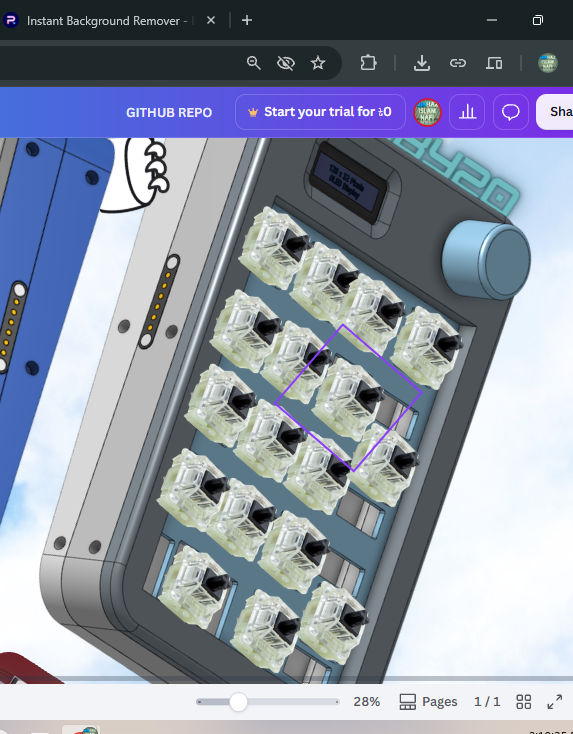
DOCS/Screenshot 2026-06-07 151941.png
