minhazislamnafi/KEEBY60-20/DOCS/Zine.png

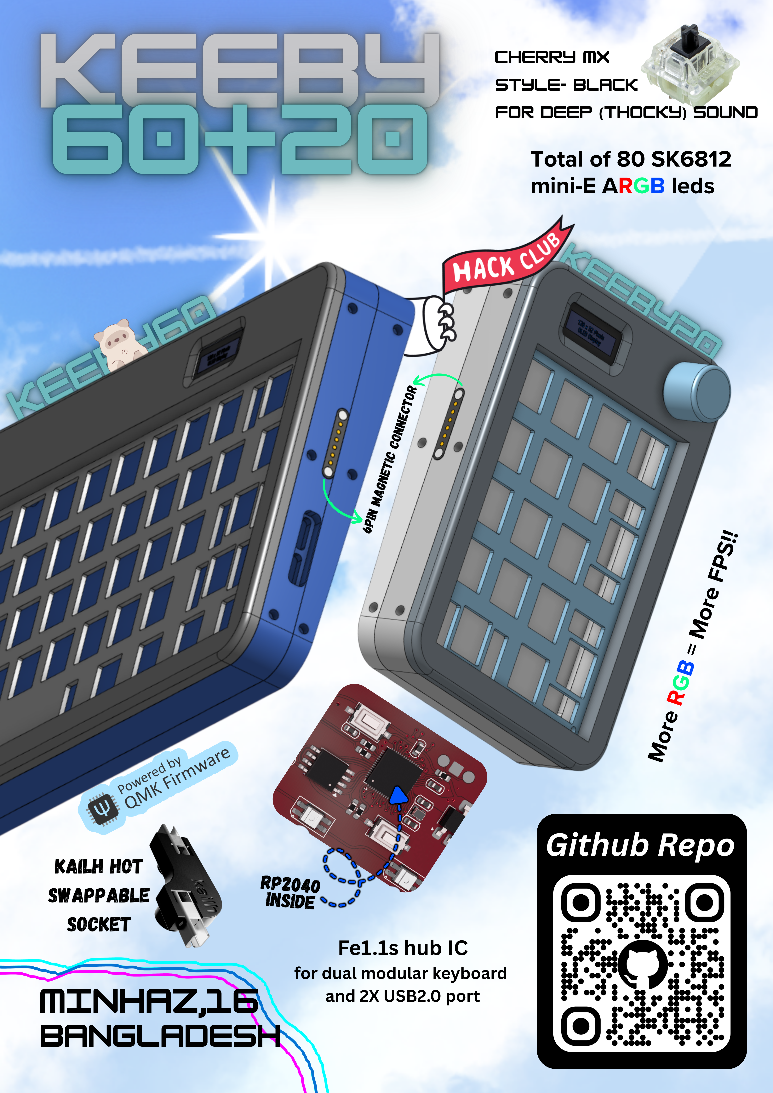
DOCS/Zine.png
